willxie/dactyl-keyboard/resources/new_features_underneath_202107.png

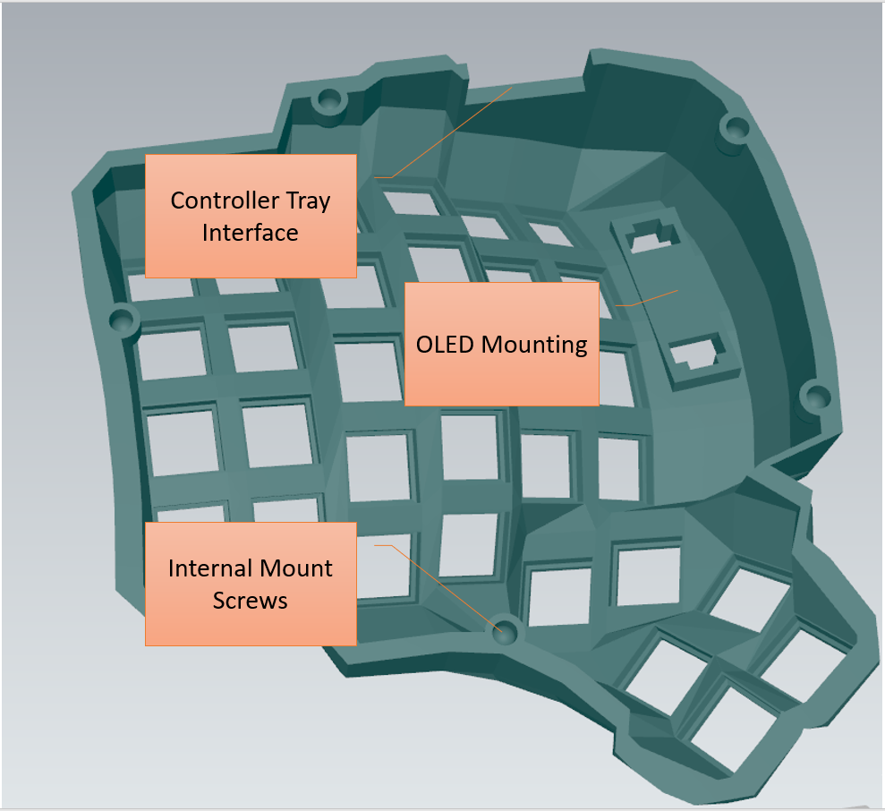
resources/new_features_underneath_202107.png
