willxie/dactyl-keyboard/resources/nice_render.png

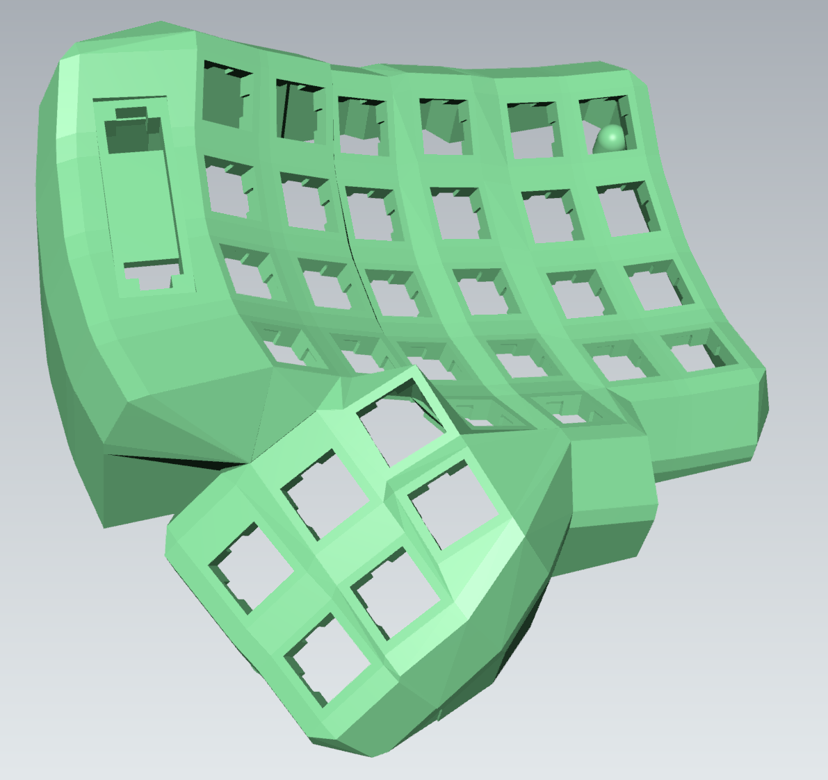
resources/nice_render.png
