willxie/dactyl-keyboard/resources/separable_thumb1.PNG

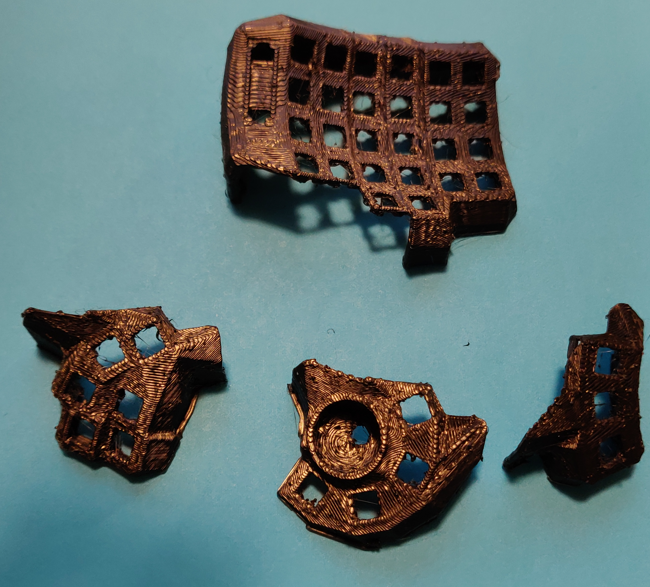
resources/separable_thumb1.PNG
