willxie/dactyl-keyboard/resources/separable_thumb2.PNG

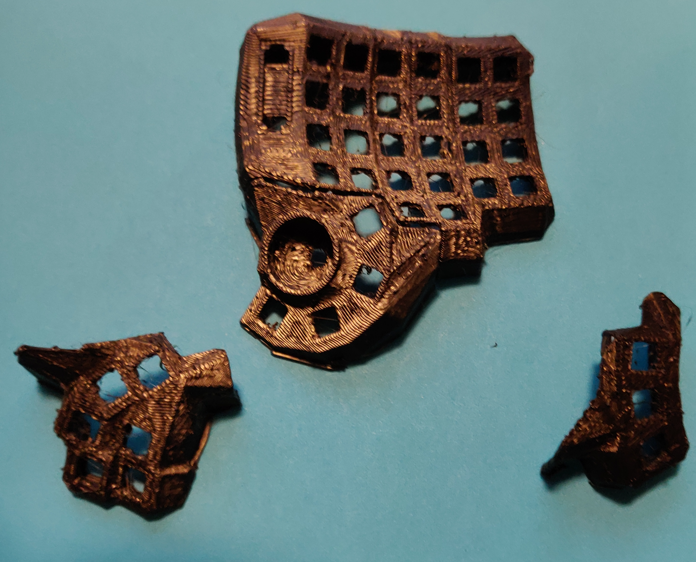
resources/separable_thumb2.PNG
