willxie/dactyl-keyboard/resources/TR_Cluster_1U.png

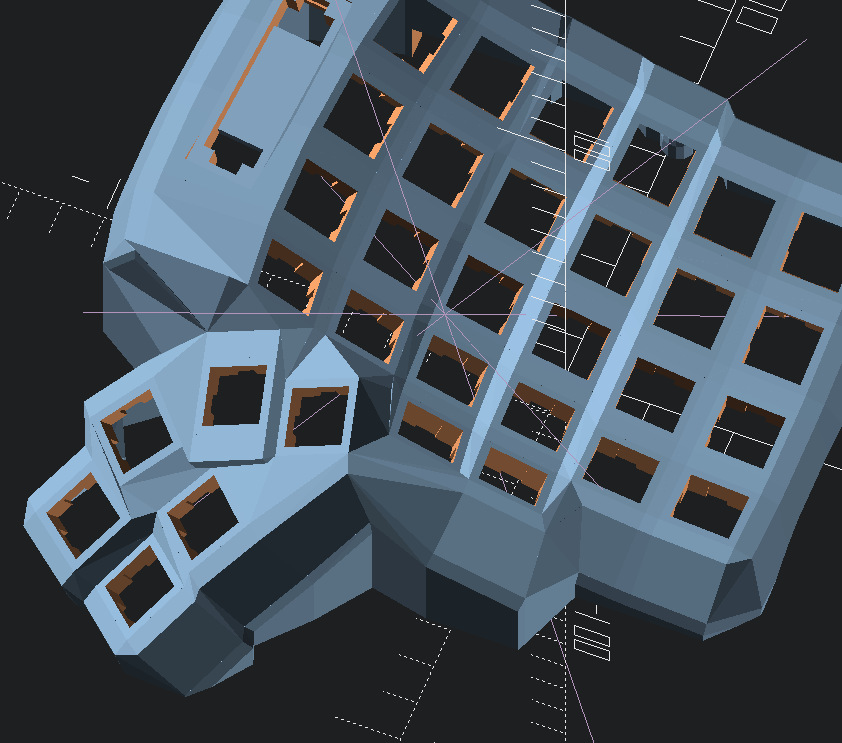
resources/TR_Cluster_1U.png
