willxie/dactyl-keyboard/resources/trackball_early_render2.png

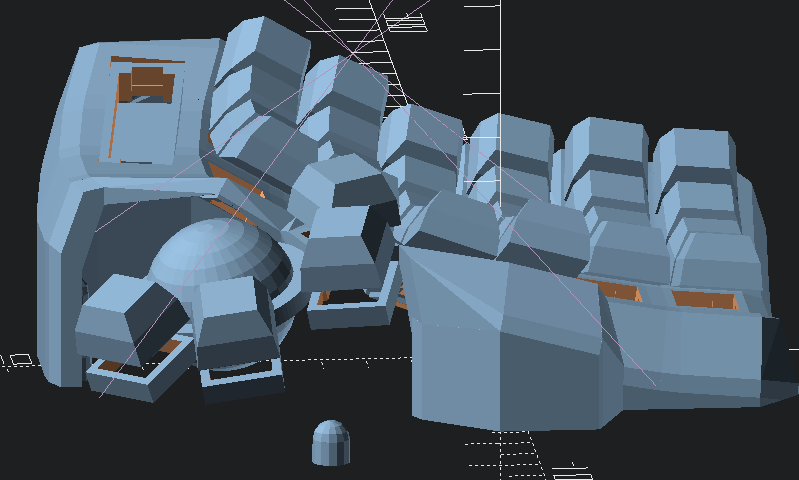
resources/trackball_early_render2.png
