willxie/dactyl-keyboard/resources/trackball_early_render.png

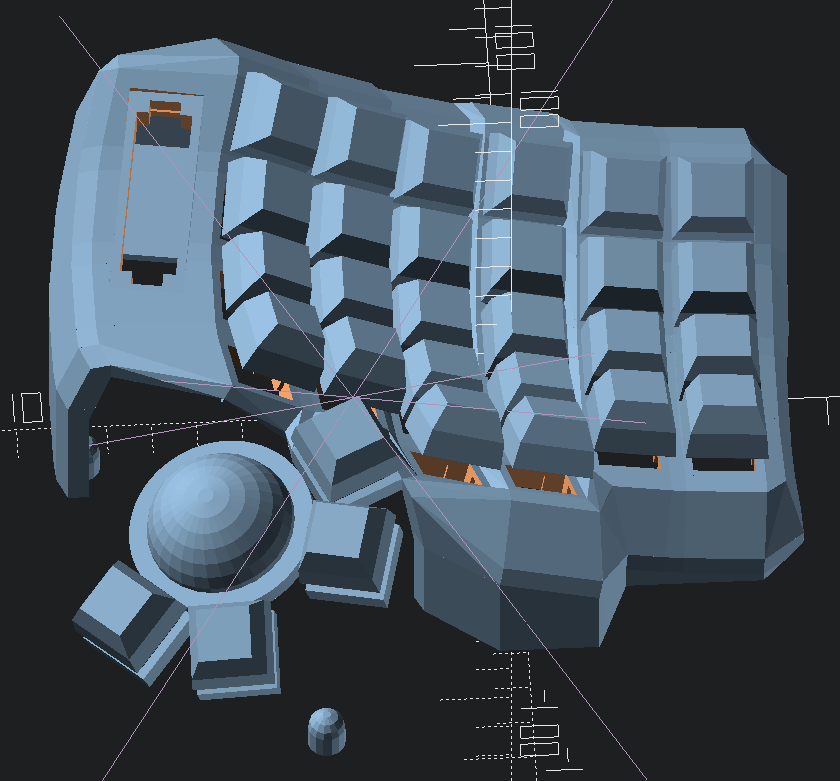
resources/trackball_early_render.png
