willxie/dactyl-keyboard/resources/Trackball_socket2.png

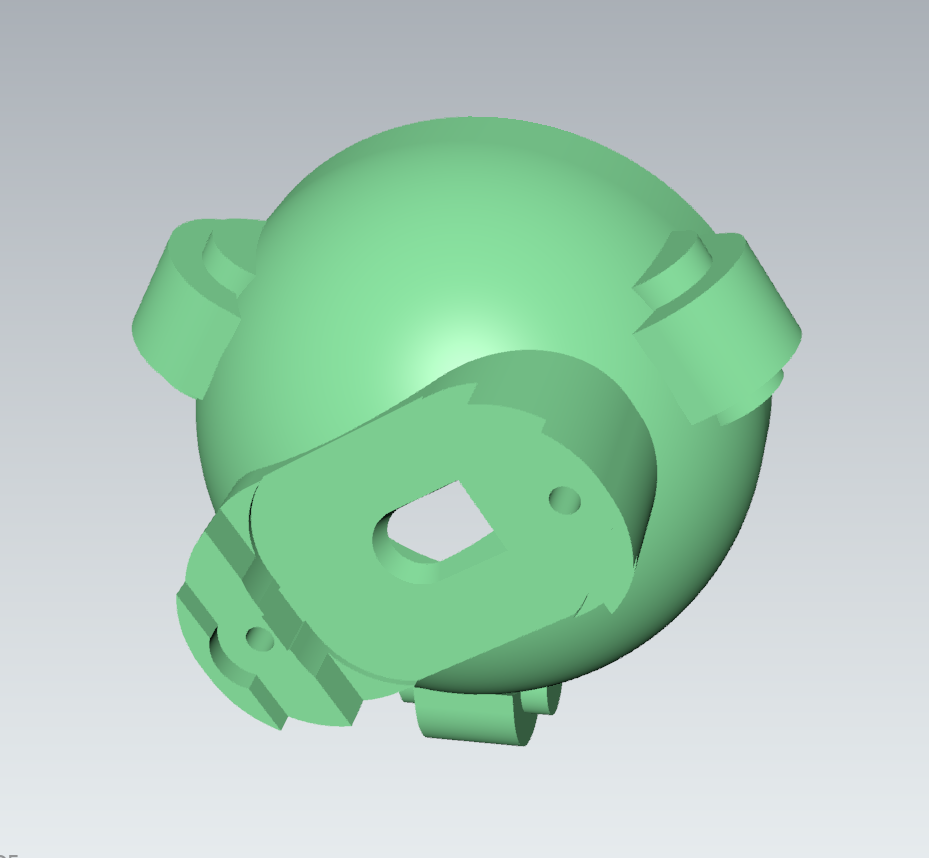
resources/Trackball_socket2.png
